connornishijima/Pixie/extras/img/3d_view.jpg

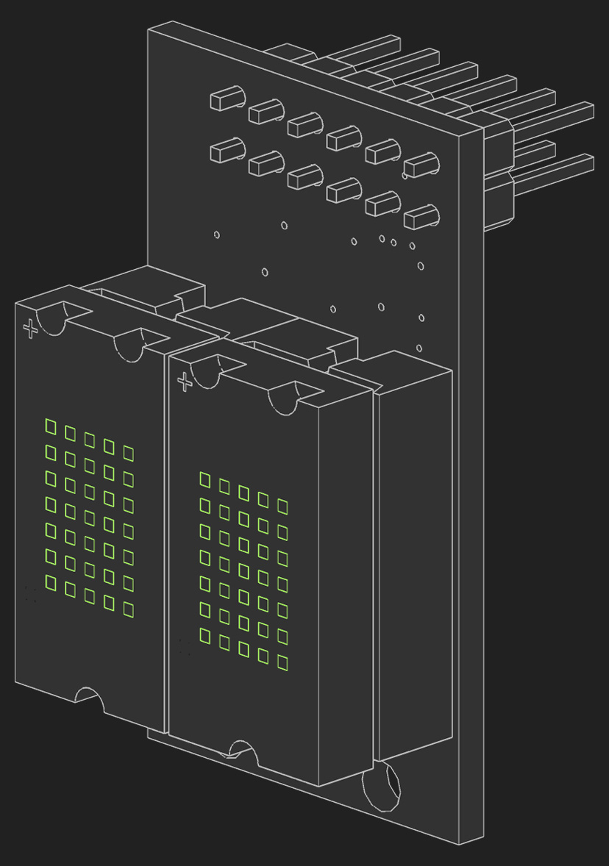
extras/img/3d_view.jpg
