connornishijima/Pixie/extras/img/dimensions_2.jpg

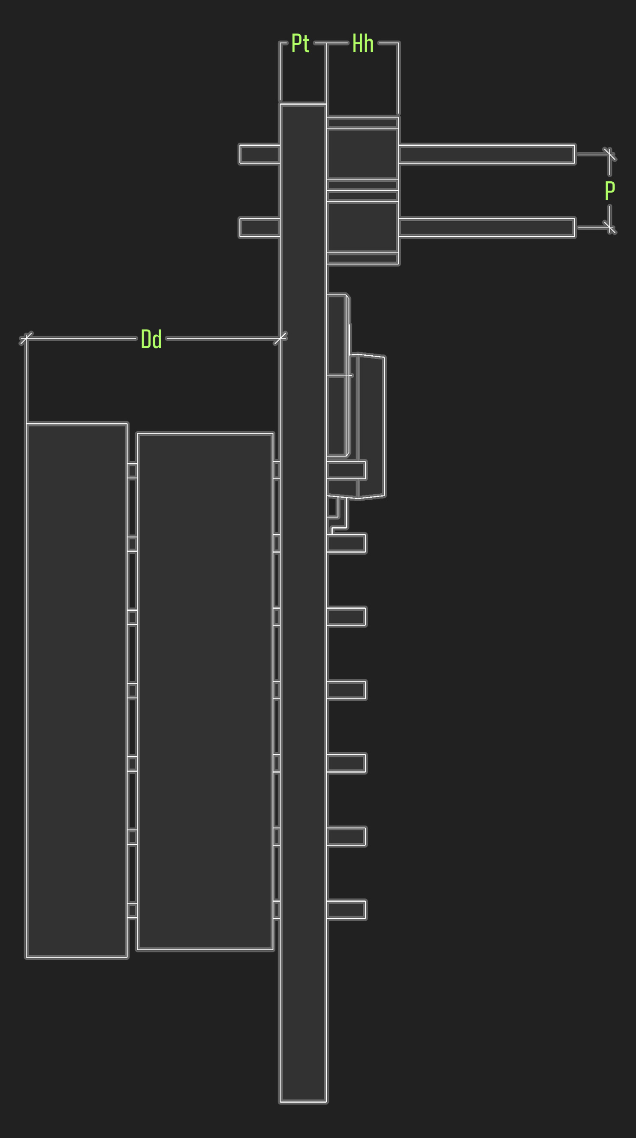
extras/img/dimensions_2.jpg
