connornishijima/Pixie/extras/img/modules.png

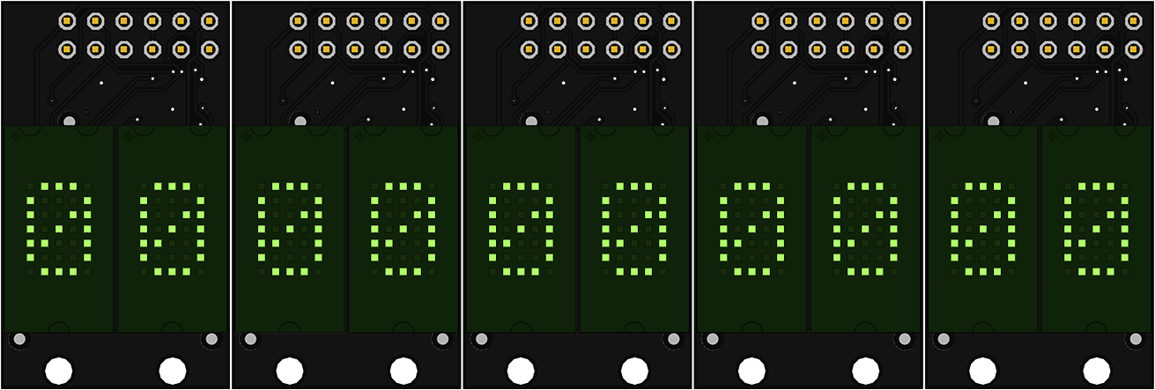
extras/img/modules.png
