connornishijima/Pixie/extras/img/timing.jpg

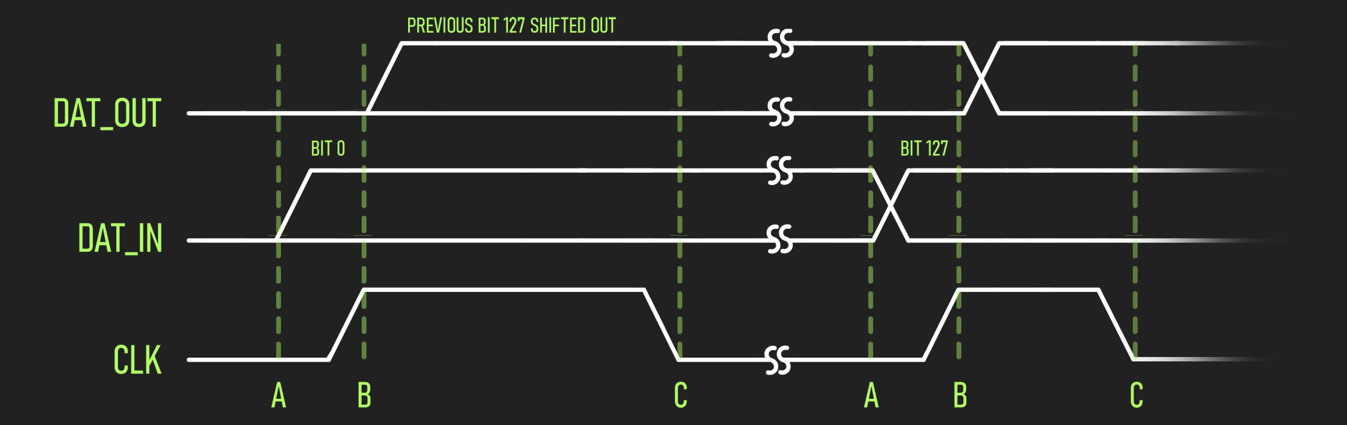
extras/img/timing.jpg
