connornishijima/Pixie/src/Pixie_Icon_Pack.h

/* PIXIE BITMAP ICONS */ 

// ARROWS
uint8_t PIX_ARROW_UP[]         = {0x04,0x02,0x7F,0x02,0x04};
uint8_t PIX_ARROW_UP_LEFT[]    = {0x1E,0x06,0x0A,0x12,0x20};
uint8_t PIX_ARROW_UP_RIGHT[]   = {0x20,0x12,0x0A,0x06,0x1E};
uint8_t PIX_ARROW_DOWN[]       = {0x10,0x20,0x7F,0x20,0x10};
uint8_t PIX_ARROW_DOWN_LEFT[]  = {0x3C,0x30,0x28,0x24,0x02};
uint8_t PIX_ARROW_DOWN_RIGHT[] = {0x02,0x24,0x28,0x30,0x3C};
uint8_t PIX_ARROW_LEFT[]       = {0x08,0x1C,0x2A,0x08,0x08};
uint8_t PIX_ARROW_RIGHT[]      = {0x08,0x08,0x2A,0x1C,0x08};
uint8_t PIX_UNDO[]             = {0x24,0x2E,0x24,0x24,0x18};
uint8_t PIX_REDO[]             = {0x18,0x24,0x24,0x2E,0x24};
uint8_t PIX_REFRESH[]          = {0x1E,0x01,0x39,0x31,0x2E};
uint8_t PIX_TRIANGLE_UP[]      = {0x10,0x18,0x1C,0x18,0x10};
uint8_t PIX_TRIANGLE_DOWN[]    = {0x04,0x0C,0x1C,0x0C,0x04};
uint8_t PIX_TRIANGLE_LEFT[]    = {0x00,0x08,0x1C,0x3E,0x00};
uint8_t PIX_TRIANGLE_RIGHT[]   = {0x00,0x3E,0x1C,0x08,0x00};

// SYMBOLS
uint8_t PIX_HEART[]            = {0x0C,0x12,0x24,0x12,0x0C};
uint8_t PIX_SMILE[]            = {0x10,0x26,0x20,0x26,0x10};
uint8_t PIX_FROWN[]            = {0x20,0x16,0x10,0x16,0x20};
uint8_t PIX_HAPPY[]            = {0x16,0x22,0x20,0x22,0x16};
uint8_t PIX_SAD[]              = {0x44,0x26,0x20,0x26,0x44};
uint8_t PIX_ANGRY[]            = {0x49,0x2A,0x20,0x2A,0x49};
uint8_t PIX_NO[]               = {0x1C,0x32,0x2A,0x26,0x1C};
uint8_t PIX_DO_NOT_ENTER[]     = {0x1C,0x36,0x36,0x36,0x1C};
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
uint8_t PIX_Z_CARON[]         = {0x44,0x65,0x56,0x4D,0x44};
uint8_t PIX_Z_OVERDOT[]       = {0x44,0x64,0x55,0x4C,0x44};

// GERMAN
uint8_t PIX_ESZETT[]          = {0x7E,0x01,0x45,0x4A,0x30};

// SLAVIC
uint8_t PIX_L_SLAVIC[]        = {0x20,0x10,0x7F,0x04,0x02};

// OLD ENGLISH
uint8_t PIX_ETH_UPPER[]       = {0x49,0x7F,0x49,0x41,0x3E};
uint8_t PIX_ETH_LOWER[]       = {0x00,0x35,0x4A,0x4D,0x38};
uint8_t PIX_THORN[]           = {0x7F,0x12,0x12,0x12,0x0C};
