connornishijima/Pixie/extras/raspberry_pi/pixie.py

import time
import spidev
spi = spidev.SpiDev()

disp_buffer = []
pixie_count = 0
disp_count  = 0
cursor_pos  = 0
bright = 0b11111111

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
E_ACUTE" : [0x38,0x56,0x55,0x54,0x18], "PIX_E_CEDILLA" : [0x0E,0x55,0x35,0x15,0x06], "PIX_E_CIRCUMFLEX" : [0x38,0x56,0x55,0x56,0x18], "PIX_E_GRAVE" : [0x38,0x54,0x55,0x56,0x18],"PIX_E_MACRON" : [0x38,0x55,0x55,0x55,0x18],"PIX_E_UMLAUT" : [0x38,0x55,0x54,0x55,0x18], "PIX_I_ACUTE" : [0x00,0x00,0x7A,0x01,0x00], "PIX_I_CIRCUMFLEX" : [0x00,0x02,0x79,0x02,0x00], "PIX_I_GRAVE" : [0x00,0x01,0x7A,0x00,0x00],"PIX_I_MACRON" : [0x00,0x02,0x7A,0x02,0x00], "PIX_I_UMLAUT" : [0x00,0x02,0x78,0x02,0x00], "PIX_O_ACUTE" : [0x38,0x44,0x46,0x45,0x38], "PIX_O_CIRCUMFLEX" : [0x38,0x46,0x45,0x46,0x38], "PIX_O_GRAVE" : [0x38,0x45,0x46,0x44,0x38],"PIX_O_MACRON" : [0x38,0x45,0x45,0x45,0x38], "PIX_O_TILDE" : [0x3A,0x45,0x46,0x45,0x38], "PIX_O_UMLAUT" : [0x38,0x45,0x44,0x45,0x38], "PIX_U_ACUTE" : [0x3C,0x40,0x42,0x21,0x7C], "PIX_U_CIRCUMFLEX" : [0x38,0x42,0x41,0x22,0x78], "PIX_U_GRAVE" : [0x3C,0x41,0x42,0x20,0x7C],"PIX_U_MACRON" : [0x3C,0x41,0x41,0x21,0x7C], "PIX_U_UMLAUT" : [0x3C,0x41,0x40,0x21,0x7C], "PIX_C_ACUTE" : [0x30,0x4A,0x49,0x48,0x00],"PIX_C_CARON" : [0x30,0x49,0x4A,0x49,0x00],"PIX_C_CEDILLA" : [0x0C,0x52,0x32,0x12,0x00],"PIX_L_CEDILLA" : [0x00,0x40,0x3F,0x00,0x00],"PIX_N_ACUTE" : [0x7C,0x08,0x06,0x05,0x78],"PIX_N_CEDILLA" : [0x1F,0x42,0x21,0x01,0x1E],"PIX_N_TILDE" : [0x7A,0x11,0x0A,0x09,0x70],"PIX_S_ACUTE" : [0x48,0x54,0x56,0x55,0x24],"PIX_S_CARON" : [0x48,0x55,0x56,0x55,0x24],"PIX_Y_UMLAUT" : [0x0C,0x51,0x50,0x51,0x3C], "PIX_Z_ACUTE" : [0x44,0x64,0x56,0x4D,0x44],"PIX_Z_CARON" : [0x44,0x65,0x56,0x4D,0x44],"PIX_Z_OVERDOT" : [0x44,0x64,0x55,0x4C,0x44],"PIX_ESZETT" : [0x7E,0x01,0x45,0x4A,0x30],"PIX_L_SLAVIC" : [0x20,0x10,0x7F,0x04,0x02],"PIX_ETH_UPPER" : [0x49,0x7F,0x49,0x41,0x3E],"PIX_ETH_LOWER" : [0x00,0x35,0x4A,0x4D,0x38],"PIX_THORN" : [0x7F,0x12,0x12,0x12,0x0C]}

def begin(num_pix):
	global disp_count
	spi.open(0,0)
	# SPI Settings
	spi.max_speed_hz = 20000 # increase or decrease speed if issues occur
	spi.mode = 0b01 # clock polarity and phase
	spi.no_cs = True # No CS pin needed

	pixie_count = num_pix
	disp_count = pixie_count*2
	total_bytes = disp_count*8
	for i in range(total_bytes):
		disp_buffer.append(0)

def delay(milliseconds):
	time.sleep(milliseconds/1000.0)

def show():
#	print("show()")
	spi.writebytes(disp_buffer)
	time.sleep(0.01)

def brightness(b):
	global disp_count
	global bright
	bright = b + 128;
	for i in range(disp_count):
		write_brightness(bright, i)

def write_brightness(br, pos):
	global disp_count
	global bright
	if pos < disp_count:
		write_col(0,      8*pos+0)
		write_col(br,     8*pos+1)
		write_col(0,      8*pos+2)

def write(input, pos = 0):
	if isinstance(input, list):
		write_icon(input[0],input[1],input[2],input[3],input[4], pos)
	else:
		input = str(input)
		length = len(input)

		for i in range(length):
			write_char(input[i], i+pos);

def write_icon(col1,col2,col3,col4,col5, pos = 0):
	write_col(0,      8*pos+0)
	write_col(bright, 8*pos+1)
	write_col(0,      8*pos+2)
	write_col(col1,  8*pos+3)
	write_col(col2,  8*pos+4)
	write_col(col3,  8*pos+5)
	write_col(col4,  8*pos+6)
	write_col(col5,  8*pos+7)

def write_col(col, pos):
#	print("write_col()")
	temp_col = col;
	try:
		disp_buffer[pos] = temp_col;
	except: # Off screen
		pass

def write_char(chr, pos):
#	print("write_char()")
	write_col(0,      8*pos+0)
	write_col(bright, 8*pos+1)
	write_col(0,      8*pos+2)
	write_col(chars[chr][0],  8*pos+3)
	write_col(chars[chr][1],  8*pos+4)
	write_col(chars[chr][2],  8*pos+5)
	write_col(chars[chr][3],  8*pos+6)
	write_col(chars[chr][4],  8*pos+7)

	set_cursor(pos+1)

def printout(input):
	global cursor_pos
	if isinstance(input, list):
		print_icon(input[0],input[1],input[2],input[3],input[4])
	else:
		input = str(input)
		pos = cursor_pos
		for item in input:
			print_char(item)

def print_char(chr):
	global cursor_pos
	pos = cursor_pos
	cursor_pos+=1

	write_col(0,      8*pos+0)
	write_col(bright, 8*pos+1)
	write_col(0,      8*pos+2)
	write_col(chars[chr][0],  8*pos+3)
	write_col(chars[chr][1],  8*pos+4)
	write_col(chars[chr][2],  8*pos+5)
	write_col(chars[chr][3],  8*pos+6)
	write_col(chars[chr][4],  8*pos+7)

def print_icon(col1,col2,col3,col4,col5):
	global cursor_pos
	pos = cursor_pos
	cursor_pos+=1

	write_col(0,      8*pos+0)
	write_col(bright, 8*pos+1)
	write_col(0,      8*pos+2)
	write_col(col1,  8*pos+3)
	write_col(col2,  8*pos+4)
	write_col(col3,  8*pos+5)
	write_col(col4,  8*pos+6)
	write_col(col5,  8*pos+7)

def push(input):
	if isinstance(input, list):
		push_icon(input[0],input[1],input[2],input[3],input[4])
	else:
		input = str(input)
		for item in input:
			push_char(item)

def push_char(chr):
	push_byte(0)
	push_byte(bright)
	push_byte(0)
	push_byte(chars[chr][0])
	push_byte(chars[chr][1])
	push_byte(chars[chr][2])
	push_byte(chars[chr][3])
	push_byte(chars[chr][4])

def push_icon(col1,col2,col3,col4,col5):
	push_byte(0)
	push_byte(bright)
	push_byte(0)
	push_byte(col1)
	push_byte(col2)
	push_byte(col3)
	push_byte(col4)
	push_byte(col5)

def push_byte(col):
	temp_col = col

	disp_buffer.pop(0)
	try:
		disp_buffer.append(temp_col)
	except:
		pass

def shift(input):
	if isinstance(input, list):
		shift_icon(input[0],input[1],input[2],input[3],input[4])
	else:
		input = str(input)
		input = input[::-1]
		for item in input:
			shift_char(item)

def shift_char(chr):
	shift_byte(chars[chr][4])
	shift_byte(chars[chr][3])
	shift_byte(chars[chr][2])
	shift_byte(chars[chr][1])
	shift_byte(chars[chr][0])
	shift_byte(0)
	shift_byte(bright)
	shift_byte(0)

def shift_icon(col1,col2,col3,col4,col5):
	shift_byte(col5)
	shift_byte(col4)
	shift_byte(col3)
	shift_byte(col2)
	shift_byte(col1)
	shift_byte(0)
	shift_byte(bright)
	shift_byte(0)

def shift_byte(col):
	temp_col = col;
	disp_buffer.insert(0, col)
	del disp_buffer[-1]

def scroll_message(input, wait_ms = 100, instant = False):
	global disp_count
	clear()
	input = str(input)
	length = len(input)

	hold_time = 1

	if instant == False:
		for c in range(length):
			chr = input[c]

			push_byte(0)
			show()
			delay(hold_time)
			push_byte(bright)
			show()
			delay(hold_time)
			push_byte(0)
			show()
			delay(hold_time)
			push_byte(chars[chr][0])
			show()
			delay(hold_time)
			push_byte(chars[chr][1])
			show()
			delay(hold_time)
			push_byte(chars[chr][2])
			show()
			delay(hold_time)
			push_byte(chars[chr][3])
			show()
			delay(hold_time)
			push_byte(chars[chr][4])
			show()
			delay(hold_time)

			delay(wait_ms)

		for i in range(disp_count):
			push_byte(0)
			show()
			delay(hold_time)
			push_byte(bright)
			show()
			delay(hold_time)
			push_byte(0)
			show()
			delay(hold_time)
			push_byte(0)
			show()
			delay(hold_time)
			push_byte(0)
			show()
			delay(hold_time)
			push_byte(0)
			show()
			delay(hold_time)
			push_byte(0)
			show()
			delay(hold_time)
			push_byte(0)
			show()
			delay(hold_time)

			delay(wait_ms)
	else:
		for c in range(length):
			chr = input[c];

			push_byte(0)
			push_byte(bright)
			push_byte(0)
			push_byte(chars[chr][0])
			push_byte(chars[chr][1])
			push_byte(chars[chr][2])
			push_byte(chars[chr][3])
			push_byte(chars[chr][4])
			show()
			delay(wait_ms)

		for i in range(disp_count):
			push_byte(0)
			push_byte(bright)
			push_byte(0)
			push_byte(0)
			push_byte(0)
			push_byte(0)
			push_byte(0)
			push_byte(0)
			show()
			delay(wait_ms)

def clear():
	global cursor_pos
#	print("clear()")
	for d in range(disp_count*8):
		disp_buffer[d] = 0;
	cursor_pos = 0;

def set_cursor(pos):
#	print("set_cursor()")
	cursor_pos = pos
